xdesig/Dateiro/Imaxes/Dateiro_Capt1.png

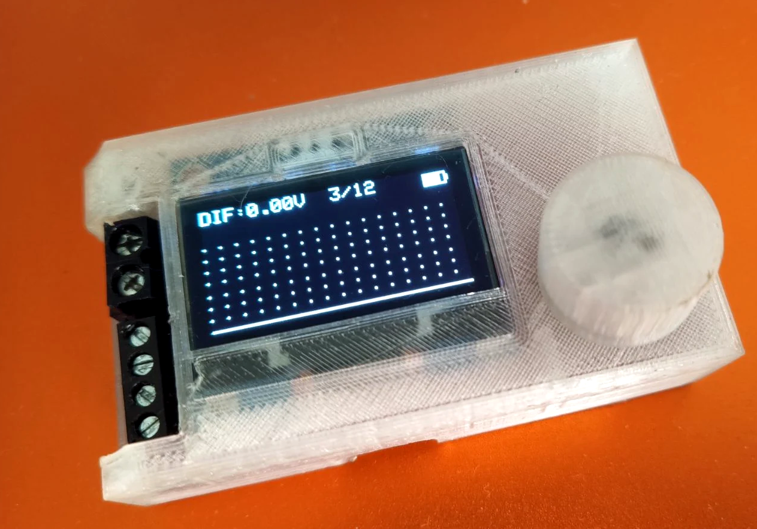
Imaxes/Dateiro_Capt1.png
