xdesig/Dateiro/Imaxes/Dateiro_Capt4.png

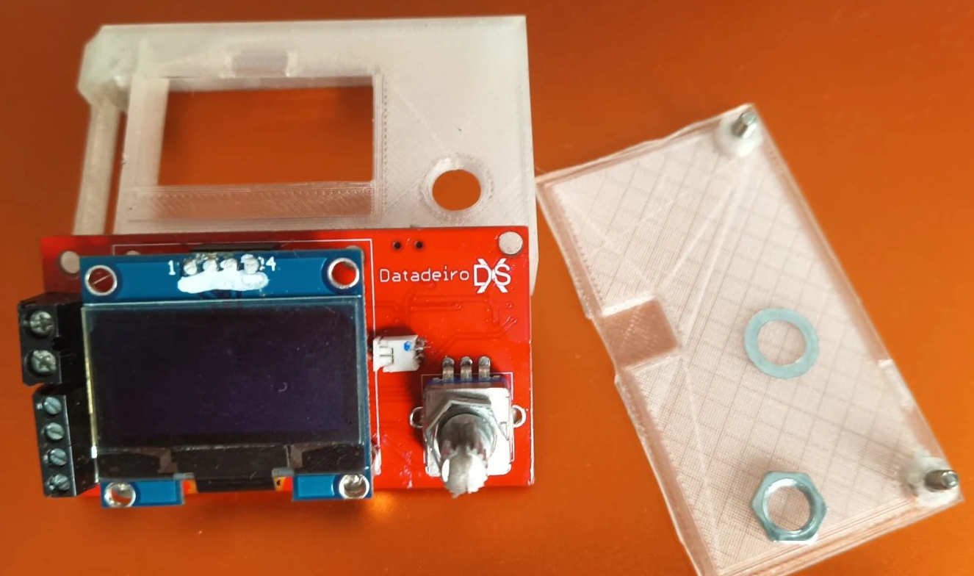
Imaxes/Dateiro_Capt4.png
