xdesig/Dateiro/Imaxes/eagleUp_MED_ESP32_C3_0002_board_bottom.png

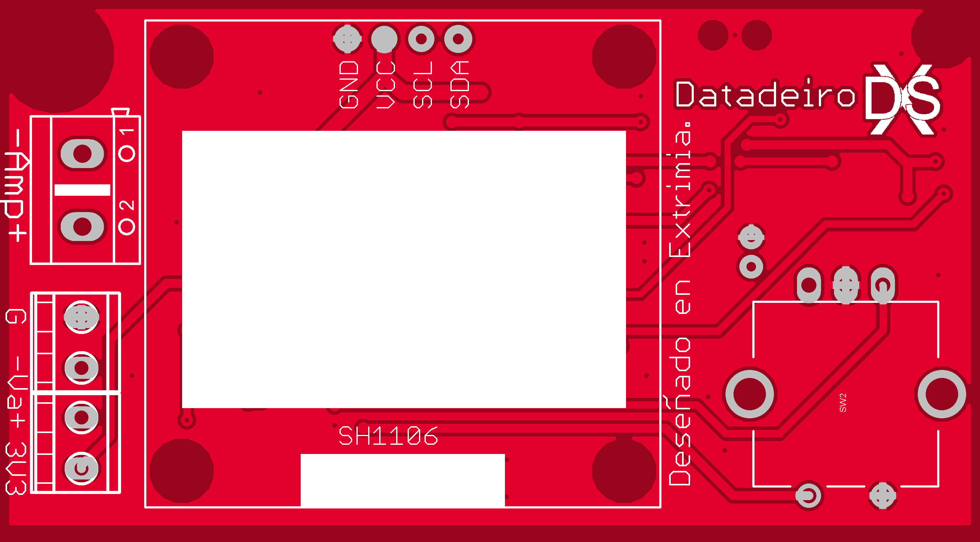
Imaxes/eagleUp_MED_ESP32_C3_0002_board_bottom.png
