xdesig/Dateiro/Imaxes/SketchUp_MED_ESP32_C3_0002.png

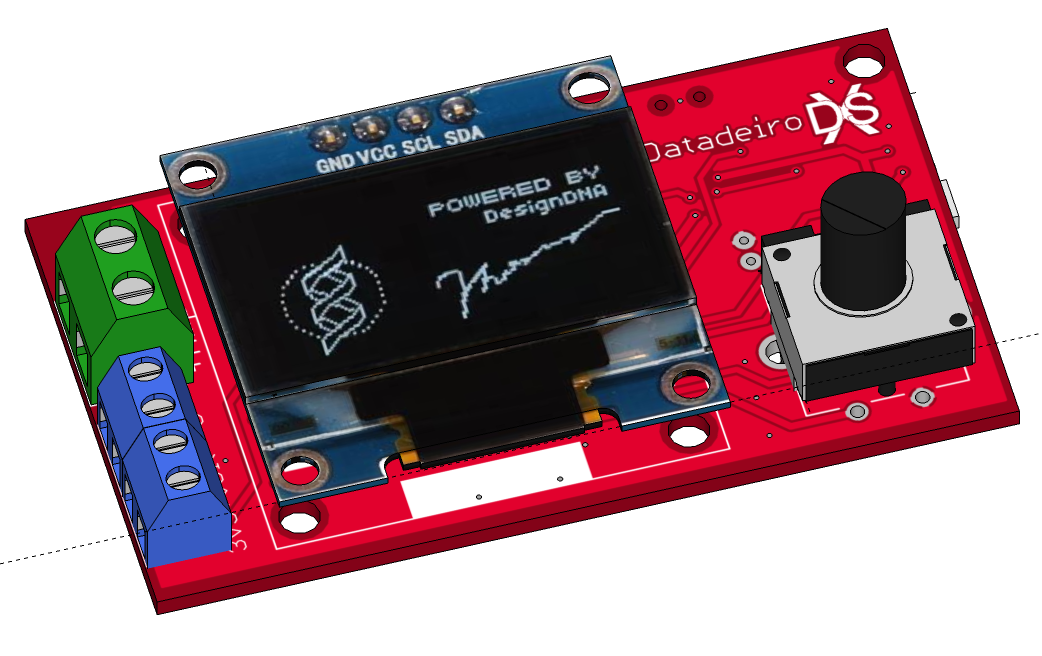
Imaxes/SketchUp_MED_ESP32_C3_0002.png
